ngtrangminhduc/Overheat-Sensor/2018_Images/Budget.jpg

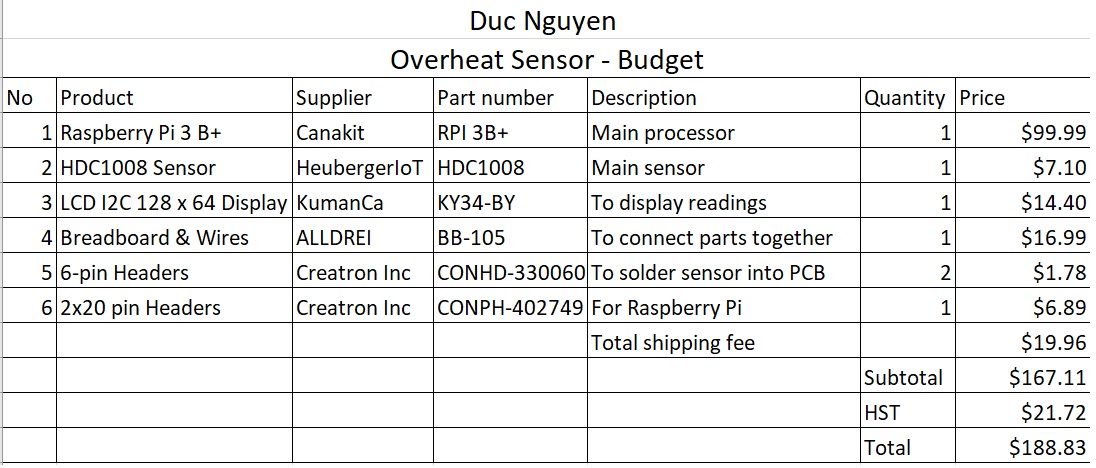
2018_Images/Budget.jpg
